jaycollett/MQTTDoorbell/Misc Project Files/Project Enclosure Images/20190217_212332.jpg

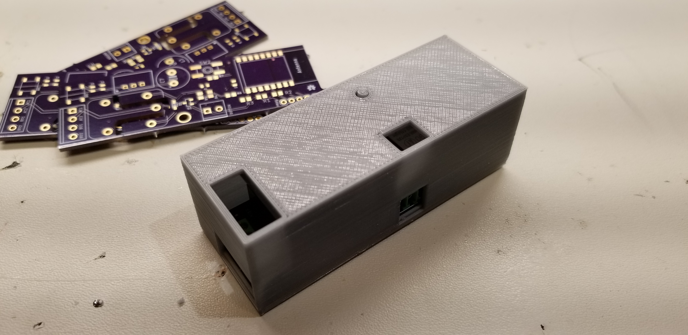
Misc Project Files/Project Enclosure Images/20190217_212332.jpg
