jaycollett/MQTTDoorbell/Misc Project Files/Project Enclosure Images/20190217_212504.jpg

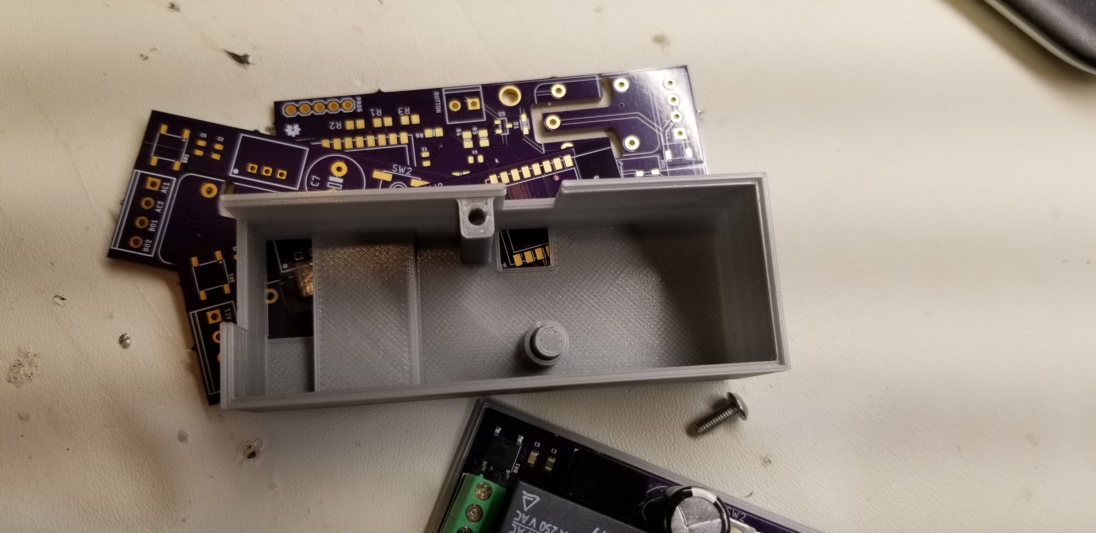
Misc Project Files/Project Enclosure Images/20190217_212504.jpg
