jaycollett/MQTTDoorbell/Misc Project Files/Project Enclosure Images/20190217_212509.jpg

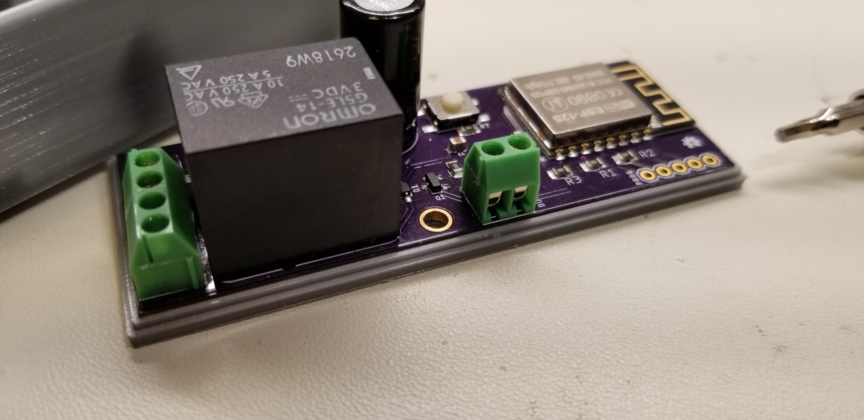
Misc Project Files/Project Enclosure Images/20190217_212509.jpg
