jaycollett/MQTTDoorbell/Misc Project Files/Project Enclosure Images/20190217_212608.jpg

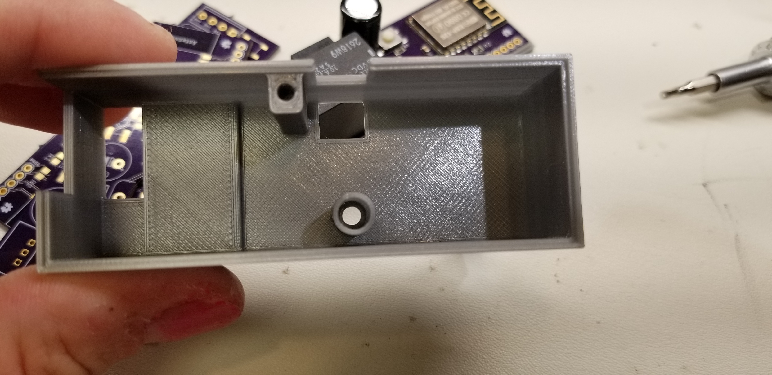
Misc Project Files/Project Enclosure Images/20190217_212608.jpg
